bschwind/key-ripper/firmware/src/hid_descriptor.rs

// TODO(bschwind) - Implement NKRO:
//                  https://www.devever.net/~hl/usbnkro
//                  https://static.wongcornall.com/ibm-capsense-usb-web/ibm-capsense-usb.html#x1-160003.3.2

#[rustfmt::skip]
pub const KEYBOARD_REPORT_DESCRIPTOR: &[u8] = &[
    0x05, 0x01,        // Usage Page (Generic Desktop Ctrls)
    0x09, 0x06,        // Usage (Keyboard)
    0xA1, 0x01,        // Collection (Application)

    // Modifier Keys
    0x05, 0x07,        //   Usage Page (Kbrd/Keypad)
    0x19, 0xE0,        //   Usage Minimum (0xE0)
    0x29, 0xE7,        //   Usage Maximum (0xE7)
    0x15, 0x00,        //   Logical Minimum (0)
    0x25, 0x01,        //   Logical Maximum (1)
    0x95, 0x08,        //   Report Count (8)
    0x75, 0x01,        //   Report Size (1)
    0x81, 0x02,        //   Input (Data,Var,Abs,No Wrap,Linear,Preferred State,No Null Position)

    // Reserved Byte
    0x95, 0x01,        //   Report Count (1)
    0x75, 0x08,        //   Report Size (8)
    0x81, 0x01,        //   Input (Const,Var,Abs,No Wrap,Linear,Preferred State,No Null Position)

    // LEDs
    0x05, 0x08,        //   Usage Page (LEDs)
    0x19, 0x01,        //   Usage Minimum (Num Lock)
    0x29, 0x05,        //   Usage Maximum (Kana)
    0x95, 0x05,        //   Report Count (5)
    0x75, 0x01,        //   Report Size (1)
    0x91, 0x02,        //   Output (Data,Var,Abs,No Wrap,Linear,Preferred State,No Null Position,Non-volatile)

    // LED Padding
    0x95, 0x01,        //   Report Count (1)
    0x75, 0x03,        //   Report Size (3)
    0x91, 0x01,        //   Output (Const,Var,Abs,No Wrap,Linear,Preferred State,No Null Position,Non-volatile)

    // Keycodes
    0x05, 0x07,        //   Usage Page (Kbrd/Keypad)
    0x19, 0x00,        //   Usage Minimum (0x00)
    0x29, 0xDD,        //   Usage Maximum (0xDD) - TODO - double check this
    0x15, 0x00,        //   Logical Minimum (0)
    0x26, 0xFF, 0x00,  //   Logical Maximum (255) - TOOD - double check max and trailing 0x00 byte
    0x95, 0x06,        //   Report Count (6)
    0x75, 0x08,        //   Report Size (8)
    0x81, 0x00,        //   Input (Data,Array,Abs,No Wrap,Linear,Preferred State,No Null Position)

    0xC0,              // End Collection
];
