bschwind/key-ripper/firmware/src/key_scan.rs

use crate::{
    key_mapping::{FN_LAYER_MAPPING, NORMAL_LAYER_MAPPING},
    NUM_COLS, NUM_ROWS,
};
use core::{convert::Infallible, ops::Deref};

use cortex_m::delay::Delay;
use embedded_hal::digital::InputPin;

use crate::{debounce::Debounce, key_codes::KeyCode};

#[derive(Clone, Copy)]
pub struct KeyScan<const NUM_ROWS: usize, const NUM_COLS: usize> {
    matrix: [[bool; NUM_ROWS]; NUM_COLS],
}

impl<const NUM_ROWS: usize, const NUM_COLS: usize> Deref for KeyScan<NUM_ROWS, NUM_COLS> {
    type Target = [[bool; NUM_ROWS]; NUM_COLS];

    fn deref(&self) -> &Self::Target {
        &self.matrix
    }
}

impl<const NUM_ROWS: usize, const NUM_COLS: usize> KeyScan<NUM_ROWS, NUM_COLS> {
    pub fn scan(
        rows: &mut [&mut dyn InputPin<Error = Infallible>; NUM_ROWS],
        columns: &mut [&mut dyn embedded_hal::digital::OutputPin<Error = Infallible>; NUM_COLS],
        delay: &mut Delay,
        debounce: &mut Debounce<NUM_ROWS, NUM_COLS>,
    ) -> Self {
        let mut raw_matrix = [[false; NUM_ROWS]; NUM_COLS];

        for (gpio_col, matrix_col) in columns.iter_mut().zip(raw_matrix.iter_mut()) {
            gpio_col.set_high().unwrap();
            delay.delay_us(1);

            for (gpio_row, matrix_row) in rows.iter_mut().zip(matrix_col.iter_mut()) {
                *matrix_row = gpio_row.is_high().unwrap();
            }

            gpio_col.set_low().unwrap();
        }

        let matrix = debounce.report_and_tick(&raw_matrix);
        Self { matrix }
    }
}

#[derive(Copy, Clone, PartialEq)]
pub struct KeyboardReport {
    pub modifier: u8,
    pub reserved: u8,
    pub leds: u8,
    pub keycodes: [u8; 6],
}

impl KeyboardReport {
    pub fn as_raw_input(&self) -> [u8; 8] {
        [
            self.modifier,
            0x0, // Reserved byte
            // Keycodes
            self.keycodes[0],
            self.keycodes[1],
            self.keycodes[2],
            self.keycodes[3],
            self.keycodes[4],
            self.keycodes[5],
        ]
    }
}

impl<const NUM_ROWS: usize, const NUM_COLS: usize> From<KeyScan<NUM_ROWS, NUM_COLS>>
    for KeyboardReport
{
    fn from(scan: KeyScan<NUM_ROWS, NUM_COLS>) -> Self {
        let mut keycodes = [0u8; 6];
        let mut keycode_index = 0;
        let mut modifier = 0;

        let mut push_keycode = |key| {
            if keycode_index < keycodes.len() {
                keycodes[keycode_index] = key;
                keycode_index += 1;
            }
        };

        // First scan for any function keys being pressed
        let mut layer_mapping = TRANSPOSED_NORMAL_LAYER_MAPPING;
        for (matrix_column, mapping_column) in scan.matrix.iter().zip(layer_mapping) {
            for (key_pressed, mapping_row) in matrix_column.iter().zip(mapping_column) {
                if mapping_row == KeyCode::Fn && *key_pressed {
                    layer_mapping = TRANSPOSED_FN_LAYER_MAPPING;
                }
            }
        }

        // Second scan to generate the correct keycodes given the activated key map
        for (matrix_column, mapping_column) in scan.matrix.iter().zip(layer_mapping) {
            for (key_pressed, mapping_row) in matrix_column.iter().zip(mapping_column) {
                if *key_pressed {
                    if let Some(bitmask) = mapping_row.modifier_bitmask() {
                        modifier |= bitmask;
                    } else {
                        push_keycode(mapping_row as u8);
                    }
                }
            }
        }

        KeyboardReport { modifier, reserved: 0, leds: 0, keycodes }
    }
}

// We need the key mappings to be transposed because the key mapping is
// defined as [[KeyCode; NUM_COLS]; NUM_ROWS] but our scanning logic
// assumes [[KeyCode; NUM_ROWS]; NUM_COLS].
pub const TRANSPOSED_NORMAL_LAYER_MAPPING: [[KeyCode; NUM_ROWS]; NUM_COLS] =
    transpose(NORMAL_LAYER_MAPPING);
pub const TRANSPOSED_FN_LAYER_MAPPING: [[KeyCode; NUM_ROWS]; NUM_COLS] =
    transpose(FN_LAYER_MAPPING);

pub const fn transpose<const NUM_ROWS: usize, const NUM_COLS: usize>(
    matrix: [[KeyCode; NUM_COLS]; NUM_ROWS],
) -> [[KeyCode; NUM_ROWS]; NUM_COLS] {
    let mut new_matrix: [[KeyCode; NUM_ROWS]; NUM_COLS] = [[KeyCode::Empty; NUM_ROWS]; NUM_COLS];

    let mut col = 0;

    while col < NUM_COLS {
        let mut row = 0;
        while row < NUM_ROWS {
            new_matrix[col][row] = matrix[row][col];
            row += 1;
        }

        col += 1;
    }

    new_matrix
}
